konqi/esp-zigbee-usb-switch/main/zcl_utility.c

/*
 * SPDX-FileCopyrightText: 2024 Espressif Systems (Shanghai) CO LTD
 *
 * SPDX-License-Identifier: CC0-1.0
 *
 * Zigbee light driver example
 *
 * This example code is in the Public Domain (or CC0 licensed, at your option.)
 *
 * Unless required by applicable law or agreed to in writing, this
 * software is distributed on an "AS IS" BASIS, WITHOUT WARRANTIES OR
 * CONDITIONS OF ANY KIND, either express or implied.
 */
#include "esp_check.h"
#include "stdio.h"
#include "string.h"
#include "zcl_utility.h"
#include <stdint.h>
#include "zcl/esp_zigbee_zcl_basic.h"

static const char *TAG = "ZCL_UTILITY";

esp_err_t esp_zcl_utility_add_ep_basic_manufacturer_info(esp_zb_ep_list_t *ep_list, uint8_t endpoint_id, zcl_basic_manufacturer_info_t *info)
{
    esp_err_t ret = ESP_OK;
    esp_zb_cluster_list_t *cluster_list = NULL;
    esp_zb_attribute_list_t *basic_cluster = NULL;

    cluster_list = esp_zb_ep_list_get_ep(ep_list, endpoint_id);
    ESP_RETURN_ON_FALSE(cluster_list, ESP_ERR_INVALID_ARG, TAG, "Failed to find endpoint id: %d in list: %p", endpoint_id, ep_list);
    basic_cluster = esp_zb_cluster_list_get_cluster(cluster_list, ESP_ZB_ZCL_CLUSTER_ID_BASIC, ESP_ZB_ZCL_CLUSTER_SERVER_ROLE);
    ESP_RETURN_ON_FALSE(basic_cluster, ESP_ERR_INVALID_ARG, TAG, "Failed to find basic cluster in endpoint: %d", endpoint_id);
    ESP_RETURN_ON_FALSE((info && info->manufacturer_name), ESP_ERR_INVALID_ARG, TAG, "Invalid manufacturer name");
    ESP_ERROR_CHECK(esp_zb_basic_cluster_add_attr(basic_cluster, ESP_ZB_ZCL_ATTR_BASIC_MANUFACTURER_NAME_ID, info->manufacturer_name));
    ESP_RETURN_ON_FALSE((info && info->model_identifier), ESP_ERR_INVALID_ARG, TAG, "Invalid model identifier");
    ESP_ERROR_CHECK(esp_zb_basic_cluster_add_attr(basic_cluster, ESP_ZB_ZCL_ATTR_BASIC_MODEL_IDENTIFIER_ID, info->model_identifier));
    if (info && info->date_code)
    {
        ESP_ERROR_CHECK(esp_zb_basic_cluster_add_attr(basic_cluster, ESP_ZB_ZCL_ATTR_BASIC_DATE_CODE_ID, info->date_code));
    }
    if (info && info->sw_build_id)
    {
        ESP_ERROR_CHECK(esp_zb_basic_cluster_add_attr(basic_cluster, ESP_ZB_ZCL_ATTR_BASIC_SW_BUILD_ID, info->sw_build_id));
    }
    // esp_zb_basic_cluster_add_attr(basic_cluster,ESP_ZB_ZCL_ATTR_BASIC_POWER_SOURCE_ID, 0x04);
    return ret;
}
